tubededentifrice/espnoise/firmware/src/noise_detector.cpp

#include "noise_detector.h"

#include "config.h"

void NoiseDetector::setSettings(const RuntimeSettings& settings) {
  settings_ = settings;
  resetHistory();
  beginSample();
}

void NoiseDetector::beginSample() {
  frameCount_ = 0;
  sampleMaximumDbfs_ = -120.0F;
}

void NoiseDetector::addFrame(float dbfs) {
  ++frameCount_;
  if (dbfs > sampleMaximumDbfs_) {
    sampleMaximumDbfs_ = dbfs;
  }
}

float NoiseDetector::sampleMaximumDbfs() const {
  return sampleMaximumDbfs_;
}

AlarmLevel NoiseDetector::sampleLevel() const {
  if (sampleMaximumDbfs_ >= settings_.redThresholdDbfsX10 / 10.0F) {
    return AlarmLevel::kRed;
  }
  if (sampleMaximumDbfs_ >= settings_.orangeThresholdDbfsX10 / 10.0F) {
    return AlarmLevel::kOrange;
  }
  if (sampleMaximumDbfs_ >= settings_.greenThresholdDbfsX10 / 10.0F) {
    return AlarmLevel::kGreen;
  }
  return AlarmLevel::kQuiet;
}

size_t NoiseDetector::frameCount() const { return frameCount_; }

void NoiseDetector::commitSample() {
  if (frameCount_ == 0) {
    return;
  }
  history_[historyWriteIndex_] = sampleMaximumDbfs_;
  const size_t historyCapacity = settings_.historySampleCount();
  historyWriteIndex_ = (historyWriteIndex_ + 1) % historyCapacity;
  if (historyCount_ < historyCapacity) {
    ++historyCount_;
  }
}

void NoiseDetector::resetHistory() {
  historyCount_ = 0;
  historyWriteIndex_ = 0;
}

size_t NoiseDetector::historyCount() const { return historyCount_; }

size_t NoiseDetector::historyCountAtOrAbove(float thresholdDbfs) const {
  size_t highCount = 0;
  for (size_t index = 0; index < historyCount_; ++index) {
    if (history_[index] >= thresholdDbfs) {
      ++highCount;
    }
  }
  return highCount;
}

size_t NoiseDetector::greenSampleCount() const {
  return historyCountAtOrAbove(settings_.greenThresholdDbfsX10 / 10.0F);
}

size_t NoiseDetector::orangeSampleCount() const {
  return historyCountAtOrAbove(settings_.orangeThresholdDbfsX10 / 10.0F);
}

size_t NoiseDetector::redSampleCount() const {
  return historyCountAtOrAbove(settings_.redThresholdDbfsX10 / 10.0F);
}

float NoiseDetector::greenSampleRatio() const {
  return historyCount_ == 0
             ? 0.0F
             : static_cast<float>(greenSampleCount()) / historyCount_;
}

float NoiseDetector::orangeSampleRatio() const {
  return historyCount_ == 0
             ? 0.0F
             : static_cast<float>(orangeSampleCount()) / historyCount_;
}

float NoiseDetector::redSampleRatio() const {
  return historyCount_ == 0
             ? 0.0F
             : static_cast<float>(redSampleCount()) / historyCount_;
}

AlarmLevel NoiseDetector::historyAlarmLevel() const {
  if (historyCount_ < settings_.historySampleCount()) {
    return AlarmLevel::kQuiet;
  }
  const size_t requiredSamples = settings_.requiredTriggerSampleCount();
  if (redSampleCount() >= requiredSamples) {
    return AlarmLevel::kRed;
  }
  if (orangeSampleCount() >= requiredSamples) {
    return AlarmLevel::kOrange;
  }
  if (greenSampleCount() >= requiredSamples) {
    return AlarmLevel::kGreen;
  }
  return AlarmLevel::kQuiet;
}
