tubededentifrice/espnoise/firmware/include/ble_service.h

#pragma once

#include <array>
#include <cstdint>

#include "config_packet.h"
#include "device_name.h"
#include "noise_analytics.h"

namespace ble_service {

constexpr char kServiceUuid[] = "3F751B85-D1AC-4699-AEEC-8B5B720B706B";
constexpr char kConfigUuid[] = "0235A089-40E1-4985-A78B-046EA4D983A9";
constexpr char kStatusUuid[] = "214F1B5A-DD35-4626-8247-FA07DA61EE64";
constexpr char kNameUuid[] = "AC1D60EF-369C-4640-8055-506A1514BD49";
constexpr char kAnalyticsUuid[] = "7D4677B7-4B75-4BC8-90A8-0954BFF64EB1";

struct Status {
  uint8_t alarmState = 0;
  bool muted = false;
  bool sampling = false;
  bool alarmActive = false;
  uint8_t errorCode = 0;
  uint32_t appliedRevision = 0;
  uint32_t fingerprint = 0;
  bool measurementValid = false;
  int16_t observationMaximumDbfsX10 = -1200;
  uint16_t measurementSequence = 0;
  uint8_t historyCount = 0;
  uint8_t greenSampleCount = 0;
  uint8_t orangeSampleCount = 0;
  uint8_t redSampleCount = 0;
};

using StatusPacket = std::array<uint8_t, 20>;

StatusPacket encodeStatus(const Status& status);

bool begin(const config_packet::Bytes& appliedPacket,
           const device_name::Value& appliedName);
bool end();
void update(uint32_t nowMs);
bool takePending(config_packet::Bytes& packet, RuntimeSettings& settings,
                 uint32_t& phoneRevision);
bool takePendingName(device_name::Value& name);
bool takeNameReadRequest();
bool takeAnalyticsRequest(uint32_t& afterSequence,
                          uint32_t& currentUtcSeconds);
void acknowledge(const config_packet::Bytes& appliedPacket,
                 const Status& status);
void acknowledgeName(const device_name::Value& appliedName);
void notifyName(const device_name::Value& appliedName);
void setStatus(const Status& status);
bool notifyAnalytics(const noise_analytics::Packet& packet);

}  // namespace ble_service
