tubededentifrice/espnoise/firmware/include/noise_detector.h

#pragma once

#include <array>
#include <cstddef>

#include "alarm_level.h"
#include "config.h"
#include "runtime_settings.h"

class NoiseDetector {
 public:
  void setSettings(const RuntimeSettings& settings);
  void beginSample();
  void addFrame(float dbfs);

  float sampleMaximumDbfs() const;
  AlarmLevel sampleLevel() const;
  size_t frameCount() const;

  void commitSample();
  void resetHistory();
  size_t historyCount() const;
  size_t greenSampleCount() const;
  size_t orangeSampleCount() const;
  size_t redSampleCount() const;
  float greenSampleRatio() const;
  float orangeSampleRatio() const;
  float redSampleRatio() const;
  AlarmLevel historyAlarmLevel() const;

 private:
  size_t historyCountAtOrAbove(float thresholdDbfs) const;

  RuntimeSettings settings_;

  size_t frameCount_ = 0;
  float sampleMaximumDbfs_ = -120.0F;
  std::array<float, config::kMaximumHistorySampleCount> history_ = {};
  size_t historyCount_ = 0;
  size_t historyWriteIndex_ = 0;
};
